iSheepsters/sheep-brain/sheepBrain/state.h

#ifndef _STATE_H
#define _STATE_H
#include "soundFile.h"

extern int msToNextSoundMin;
extern int msToNextSoundMax;

enum State {
  Bored,
  Attentive,
  Riding,
  ReadyToRide,
  NotInTheMood,
  Violated,
};

extern unsigned long timeEnteredCurrentState;

extern void setupState();
extern void updateState();
extern void logState();
extern boolean privateSensorEnabled();
class SheepState {
  public:
    virtual SheepState * update() = 0;
    const char * const name;
    const enum State state;
    uint16_t timeStateStarted = 0;
    unsigned long timeInState = 0;

    SoundCollection & ambientSounds;
    SoundCollection & getInitialSounds() {
      if (initialSounds.available()) return initialSounds;
      return ambientSounds;
    }
    SheepState(enum State st, const char * n, SoundCollection & s)
      : state(st), name(n), initialSounds(s), ambientSounds(s) {};
    SheepState(enum State st, const char * n, SoundCollection & s, SoundCollection & ambient)
      : state(st), name(n), initialSounds(s), ambientSounds(ambient) {};
    boolean playAmbientSound(unsigned long now);
  private:
    SoundCollection & initialSounds;

};

extern SheepState * currentSheepState;


class BoredState : public SheepState {
  public:
    BoredState() : SheepState(Bored, "Bored", boredSounds) {};
    SheepState * update();

};

class AttentiveState : public SheepState {
  public:
    AttentiveState() : SheepState(Attentive, "Attentive", firstTouchSounds, attentiveSounds) {};
    SheepState * update();
};

class ReadyToRideState : public SheepState {
  public:
    ReadyToRideState() : SheepState(ReadyToRide, "Ready to ride", readyToRideSounds) {};
    SheepState * update();
};

class RidingState : public SheepState {
  public:
    RidingState() : SheepState(Riding, "Riding", ridingSounds) {};

    SheepState * update();
};

class NotInTheMoodState : public SheepState {
  public:
    NotInTheMoodState() : SheepState(NotInTheMood, "Not in the mood", notInTheMoodSounds) {};
    SheepState * update();
};


class ViolatedState : public SheepState {
  public:
    ViolatedState() : SheepState(Violated, "Violated", violatedSounds) {};
    SheepState * update();
};

#endif
