iSheepsters/sheep-brain/sheepBrain/soundFile.cpp

#include <Arduino.h>
#include "soundFile.h"
#include "sound.h"
#include "printf.h"
#include "util.h"

//#include <MemoryFree.h>
#include <SPI.h>
#include <SdFat.h>

#define CARDCS          5     // Card chip select pin

int currentSoundPriority = 0;

const int PATH_BUFFER_LENGTH = 100;
char pathBuffer[PATH_BUFFER_LENGTH];

boolean isMusicFile(const char * name) {

  const char *suffix = strrchr(name, '.');
  if (name[0] == '_')
    return false;

  if (!allowRrated && (name[0] == 'r' || name[0] == 'R')) return false;
  if ( strcmp(suffix, ".MP3") == 0 || strcmp(suffix, ".mp3") == 0)
    return true;
  Serial.print("non-music file: \"");
  Serial.print(name);
  Serial.println("\"");
  return false;
}

SoundCollection::SoundCollection(uint8_t pri) : priority (pri) {
  strncpy(name, "", 13);
  count = 0;
}

boolean SoundCollection::loadCommon(const char * s) {
  strncpy(name, s, 13);
  myprintf(Serial, "opening %s\n", name);

  File dir = SD.open(name);
  myprintf(Serial, "opened %s\n", name);

  common = true;
  return load(dir);
}
char buf[FILE_NAME_LENGTH];

boolean SoundCollection::load(const char * s) {
  strncpy(name, s, 13);
  snprintf(buf, 30, "%d/%s", sheepNumber, name);
  myprintf(Serial, "opening %s\n", buf);
  File dir = SD.open(buf);
  bool result =  load(dir);
  if (result) {
    myprintf(Serial, "got %d sounds for %s\n", count, name);
  } else
    myprintf(Serial, "error loading sounds for %s\n", name);
  return result;
}



boolean SoundCollection::load(File dir, File script) {
  uint16_t i = 0;
  char txt[100];
  char *s = txt;
  File check;
  while (i < MAX_SOUND_FILES) {
    int len = script.fgets(txt, 100);
    if (len <= 0) break;
    if (txt[0] == '#')
      continue;
    char * term = strchr(txt, '\t');
    if (term != NULL)
      *term = '\0';
    else {
      term = strchr(txt, '\n');
      if (term != NULL)
        *term = '\0';
    }

    if (!isMusicFile(txt)) {
      myprintf(Serial, "Skipping non-music file \"%s\" from script\n", txt);
      continue;
    }
    if (check.open(&dir, s, O_READ)) {
      myprintf(Serial, "Loading #%d  \"%s\" from script, %d bytes\n", i, txt, check.fileSize());
      check.close();
      strncat(files[i].name, txt, FILE_NAME_LENGTH);
      files[i].collection = this;
      files[i].lastPlaying = 0;
      files[i].duration = 0;
      files[i].lastStarted = 0;
      i++;

    } else
      myprintf(Serial, "Could not open \"%s\" from script\n", txt);
  }
  script.close();
  count = i;
  scripted = true;
  nextFile = 0;
  return i > 0;
}

boolean SoundCollection::load(File dir) {
  count = 0;
  if (!dir.isDirectory()) {
    Serial.print(name);
    Serial.println(" is not a directory");
    dir.close();
    return false;
  }

  File script;
  if (script.open(&dir, "script.txt", O_READ)) {
    myprintf(Serial, "Loading script for %s\n", name);
    if (load(dir, script))
      return true;
  }

  Serial.println("Scanning all files");
  dir.rewind();
  uint16_t i = 0;
  char nm[30];
  while (i < MAX_SOUND_FILES) {
    File entry = dir.openNextFile();
    if (!entry) {
      break;
    }

    entry.getName(nm, 30);
    Serial.println(nm);
    if (!entry.isDirectory() && isMusicFile(nm)) {
      entry.getName(files[i].name, FILE_NAME_LENGTH);
      files[i].collection = this;
      files[i].lastPlaying = 0;
      files[i].duration = 0;
      files[i].lastStarted = 0;
      i++;
    }
    entry.close();
  }
  count = i;
  nextFile = 0;
  myprintf(Serial, "Found %d files for %s\n", count, name);
  // myprintf(Serial, "Free memory = %d\n", freeMemory());
  dir.close();
  return true;
}

void SoundCollection::list() {

  for (int i = 0; i < count; i++) {
    myprintf(Serial, "%s\n", files[i].name);
  }
}

uint16_t ago( unsigned long t,  unsigned long now) {
  return (now - t) / 1000;
}


void SoundCollection::verboseList(unsigned long now, boolean ambientSound) {


  Serial.println( "  duration   started   playing  eligable name");
  for (int i = 0; i < count; i++) {
    myprintf(Serial, "%10d%10d%10d     %s %d.mp3\n", files[i].duration, ago(files[i].lastStarted, now),
             ago(files[i].lastPlaying,  now),
             files[i].eligibleToPlay(now, ambientSound) ? " true" : "false",
             i);

  }
}

boolean soundPlayedRecently(unsigned long now) {
  return lastSoundPlaying + 10000L > now && now > 18000;
}

unsigned long nextVerboseList = 0;
boolean SoundCollection::playSound(unsigned long now, boolean ambientSound) {
  if (printInfo())
    myprintf(Serial, "trying to play sound for %s\n", name);
  if (ambientSound && soundPlayedRecently(now)) {
    if (printInfo()) {
      Serial.print("Too soon for any sound from ");
      Serial.println(name);
    }
    return false;
  }
  SoundFile *s = chooseSound(now, ambientSound);
  if (s == NULL) {
    if (ambientSound)
      Serial.print("No ambient sound found for ");
    else
      Serial.print("No sound found for ");
    Serial.println(name);


    myprintf(Serial, "Last sound %d\n", ago(lastSoundPlaying, now));
    if (nextVerboseList < now) {
      verboseList(now, ambientSound);
      nextVerboseList = now + 30000;
    }
    return false;
  };
  slowlyStopMusic();
  musicPlayerFullVolume();

  boolean result = false;
  if (common)
    result = playFile("%s/%s", name, s->name  );
  else
    result = playFile("%d/%s/%s", sheepNumber, name, s->name  );
  if (!result) {
    myprintf(Serial, "Could not start %s/%s\n", name, s->name  );
    musicPlayerNoVolume();
    return false;
  } else {
    if (printInfo())
      myprintf(Serial, "Starting %s/%s at %d\n", name, s->name, now);
    s->lastStarted = s->lastPlaying = now;
    currentSoundFile = s;
    currentSoundPriority = priority;
    return true;
  }

}


// If ambientSound is false, always return something
SoundFile * SoundCollection::leastRecentlyPlayed(unsigned long now,
    boolean ambientSound) {

  if (printInfo())
    myprintf(Serial, "finding least recently played %s\n", name);

  SoundFile * candidate = NULL;
  unsigned long bestTime = 0xfffffff;
  int offset = random(count);
  for (int i = 0; i < count; i++) {
    int index = (i + offset) % count;
    SoundFile *s = &(files[index]);
    if (s->lastPlaying == 0)
      return s;
    if (s->eligibleToPlay(now, ambientSound) && bestTime > s->lastPlaying) {
      candidate = s;
      bestTime = s->lastPlaying;
    }
  }
  if (candidate != NULL || ambientSound)
    return candidate;
  bestTime = 0xfffffff;
  for (int i = 0; i < count; i++) {
    int index = (i + offset) % count;
    SoundFile *s = &(files[index]);
    if (bestTime > s->lastPlaying) {
      candidate = s;
      bestTime = s->lastPlaying;
    }
  }
  return candidate;
}


SoundFile * SoundCollection::chooseSound(unsigned long now,  boolean ambientSound) {
  if (count == 0) return NULL;

  if (scripted) {
    if (printInfo()) {
      myprintf(Serial, "using script entry %d\n", nextFile);
    }
    SoundFile * f = &(files[nextFile]);
    nextFile++;
    if (nextFile >= count)
      nextFile = 0;
    return f;
  }

  if (this == & violatedSounds)
    ambientSound = false;
  if (random(3) <= 1) {
    // return first eligable sound
    int firstChoice = random(count);

    int i = firstChoice;
    while (true) {
      SoundFile *s = &(files[i]);
      if (s->eligibleToPlay(now, ambientSound))
        return s;

      i = (i + 1) % count;
      if (i == firstChoice) {
        break;
      }
    }
  }
  return leastRecentlyPlayed(now, ambientSound);
}

const boolean debug_eligible = false;
boolean SoundFile::eligibleToPlay(unsigned long now, boolean ambientSound) {
  if (now == 0) {
    if (debug_eligible) myprintf(Serial, "%s eligable, not played before\n", name);
    return true;
  }
  uint32_t minimumQuietTime = 10000;
  if (ambientSound && lastSoundPlaying + minimumQuietTime > now)
    return false;

  unsigned long d = duration;
  if (d == 0) d = 5000;

  uint32_t minimumRepeatTime = d * 2 + 120000L;

  boolean result = lastPlaying == 0 || lastPlaying + minimumRepeatTime < now;
  if (debug_eligible) { // list reasons
    if (result) {
      if (lastPlaying == 0)
        myprintf(Serial, "%s eligable: not played before\n",  name);
      else
        myprintf(Serial, "%s eligable: Last playing %d seconds ago; %d minimum\n",
                 name, (now - lastPlaying) / 1000, minimumRepeatTime / 1000);
      if (ambientSound) myprintf(Serial, "  last sound %d seconds ago, minimum quiet %d seconds\n",
                                   (now - lastSoundPlaying) / 1000, minimumQuietTime / 1000);
    } else if (false) {
      myprintf(Serial, "%s not eligable: Last playing %d seconds ago; %d minimum\n",
               name, (now - lastPlaying) / 1000, minimumRepeatTime / 1000);
      if (ambientSound) myprintf(Serial, "  last sound %d seconds ago, minimum quiet %d seconds\n",
                                   (now - lastSoundPlaying) / 1000, minimumQuietTime / 1000);

    }
  }
  return result;
}


SoundFile * currentSoundFile = NULL;

#define CARDCS 5
#define SPI_SPEED SD_SCK_MHZ(4)

boolean setupSD() {
  if (!SD.begin(CARDCS, SPI_SPEED)) {
    Serial.println(F("SD failed, or not present"));
    if (SD.card()->errorCode()) {
      Serial.println(
        F( "\nSD initialization failed.\n"
           "Do not reformat the card!\n"
           "Is the card correctly inserted?\n"
           "Is chipSelect set to the correct value?\n"
           "Does another SPI device need to be disabled?\n"
           "Is there a wiring/soldering problem?\n"));

      Serial.println(int(SD.card()->errorCode()));
      Serial.println(int(SD.card()->errorData()));
      return false;
    }
  }

  Serial.println("SD OK!");
  myprintf(Serial, "size of SoundFile is %d\n", sizeof(SoundFile));


  // list files
  // printDirectory(SD.open("/"), 0);
  return true;
}




/// File listing helper
void printDirectory(File dir, int numTabs) {
  while (true) {
    char buf[40];
    File entry = dir.openNextFile();
    if (! entry) {
      // no more files
      //Serial.println("**nomorefiles**");
      break;
    }
    for (uint8_t i = 0; i < numTabs; i++) {
      Serial.print('\t');
    }
    entry.getName(buf, 40);
    Serial.print(buf);
    if (entry.isDirectory()) {
      Serial.println("/");
      printDirectory(entry, numTabs + 1);
    } else {
      // files have sizes, directories do not
      Serial.print("\t\t");
      Serial.println(entry.size(), DEC);
    }
    entry.close();
  }
}

void loadPerSheepSounds() {
  Serial.println("Loading sound files");
  //myprintf(Serial, "Free memory = %d\n", freeMemory());
  boredSounds.load("BORED");
  generalSounds.load("GENERAL");
  firstTouchSounds.load("TOUCHED");
  attentiveSounds.load("ATTNT");
  
    ridingSounds.load("RIDNG");
    readyToRideSounds.load("RDRID");
    endOfRideSounds.load("EORID");
    notInTheMoodSounds.load("NMOOD");
    violatedSounds.load("VIOLT");
    inappropriateTouchSounds.load("INAPP");
    seperatedSounds.load("SEPRT");
  
 // myprintf(Serial, "Free memory = %d\n", freeMemory());

}
