iSheepsters/sheep-brain/sheepBrain/comm.cpp

#include <Arduino.h>
#include <Wire.h>
#include "comm.h"
#include "printf.h"
#include "Print.h"
#include "util.h"
#include "touchSensors.h"
#include "scheduler.h"


const uint8_t commAddress = 0x44;

const uint8_t rebootStarted = 255;
const uint8_t rebootActivity = 254;

CommData commData;
ActivityData activityData;
unsigned long nextComm = 0;
uint8_t lastActivity = 0;

void setupComm() {
  commData.sheepNum = sheepNumber;
  addScheduledActivity(100, sendComm, "comm");
}


void getLastActivity() {

  int received = Wire.requestFrom(commAddress, sizeof(ActivityData));
  myprintf(Serial, "Requesting last activity, received %d bytes\n", received);
  activityData.reboots = 17;
  uint8_t * p = (uint8_t *) & activityData;
  if (received != sizeof(ActivityData)) {
    myprintf(Serial, "Expected %d bytes\n", sizeof(ActivityData));
    return;
  }
  for (int i = 0; i < received; i++)
    * (p++) = Wire.read();
  myprintf(Serial, "%d reboots, %d lastActivity, %d lastSubActivity\n",
           activityData.reboots,
           activityData.lastActivity,
           activityData. subActivity);
  myprintf(Serial, "%d seconds since last activity, %d seconds since slave reboot\n",
           activityData. secondsSinceLastActivity,
           activityData. secondsSinceBoot);
}

void sendBoot() {
  Serial.println("Sending boot");
  sendActivity(rebootStarted);
  delay(1);
  sendActivity(rebootActivity);
}

volatile uint8_t currentSubActivity;
uint8_t sendActivity(uint8_t activity) {
  if (activity == lastActivity && currentSubActivity == 0)
    return 0;
  lastActivity = activity;
  currentSubActivity = 0;
  Wire.beginTransmission(commAddress);
  Wire.write(57);
  Wire.write(activity);
  Wire.write(0);
  uint8_t result = Wire.endTransmission();
  return result;
}

uint8_t sendSubActivity(uint8_t subActivity) {
  currentSubActivity = subActivity;
  Wire.beginTransmission(commAddress);
  Wire.write(57);
  Wire.write(lastActivity);
  Wire.write(subActivity);
  uint8_t result = Wire.endTransmission();
  return result;
}

void sendComm() {

  unsigned long now = millis();
  if (  commData.state != currentSheepState->state
        || commData.currTouched != currTouched
        || nextComm < now) {
    nextComm = now + 1000;
 
    commData.state = currentSheepState->state;
    uint8_t touched = currTouched;
    if (sheepNumber == 9 || sheepNumber == 13) {

      uint8_t t = swapLeftRightSensors(touched);
      //myprintf(Serial, "touch %02x -> %02x\n", touched, t);
      touched = t;
    }
    commData.currTouched = touched;

      commData.backTouchQuality = millisToSecondsCapped(qualityTime(BACK_SENSOR));
    commData.headTouchQuality = millisToSecondsCapped(qualityTime(HEAD_SENSOR));
    commData.activated =  isActive() ? Active : Inactive ;
    uint8_t * p = (uint8_t *)&commData;
    if (false) {
      Serial.print("Sending ");
      for (int i = 0; i < sizeof(CommData); i++) {
        myprintf(Serial, "%02x ", p[i]);
      }
      Serial.println();
    }

    noInterrupts();
    Wire.beginTransmission(commAddress);

    Wire.write(42); // check byte
    Wire.write(p, sizeof(CommData));

    Wire.flush();
    uint8_t result = Wire.endTransmission();
    interrupts();
    delay(1);
    return;
  }
}

/**
   I2C_ClearBus
   (http://www.forward.com.au/pfod/ArduinoProgramming/I2C_ClearBus/index.html)
   (c)2014 Forward Computing and Control Pty. Ltd.
   NSW Australia, www.forward.com.au
   This code may be freely used for both private and commerical use
*/

/**
   This routine turns off the I2C bus and clears it
   on return SCA and SCL pins are tri-state inputs.
   You need to call Wire.begin() after this to re-enable I2C
   This routine does NOT use the Wire library at all.

   returns 0 if bus cleared
           1 if SCL held low.
           2 if SDA held low by slave clock stretch for > 2sec
           3 if SDA held low after 20 clocks.
*/
int I2C_ClearBus() {
#if defined(TWCR) && defined(TWEN)
  TWCR &= ~(_BV(TWEN)); //Disable the Atmel 2-Wire interface so we can control the SDA and SCL pins directly
#endif

  pinMode(SDA, INPUT_PULLUP); // Make SDA (data) and SCL (clock) pins Inputs with pullup.
  pinMode(SCL, INPUT_PULLUP);

  delay(500);  // Wait 2.5 secs. This is strictly only necessary on the first power
  // up of the DS3231 module to allow it to initialize properly,
  // but is also assists in reliable programming of FioV3 boards as it gives the
  // IDE a chance to start uploaded the program
  // before existing sketch confuses the IDE by sending Serial data.

  boolean SCL_LOW = (digitalRead(SCL) == LOW); // Check is SCL is Low.
  if (SCL_LOW) { //If it is held low Arduno cannot become the I2C master.
    return 1; //I2C bus error. Could not clear SCL clock line held low
  }

  boolean SDA_LOW = (digitalRead(SDA) == LOW);  // vi. Check SDA input.
  int clockCount = 20; // > 2x9 clock

  while (SDA_LOW && (clockCount > 0)) { //  vii. If SDA is Low,
    clockCount--;
    // Note: I2C bus is open collector so do NOT drive SCL or SDA high.
    pinMode(SCL, INPUT); // release SCL pullup so that when made output it will be LOW
    pinMode(SCL, OUTPUT); // then clock SCL Low
    delayMicroseconds(10); //  for >5uS
    pinMode(SCL, INPUT); // release SCL LOW
    pinMode(SCL, INPUT_PULLUP); // turn on pullup resistors again
    // do not force high as slave may be holding it low for clock stretching.
    delayMicroseconds(10); //  for >5uS
    // The >5uS is so that even the slowest I2C devices are handled.
    SCL_LOW = (digitalRead(SCL) == LOW); // Check if SCL is Low.
    int counter = 20;
    while (SCL_LOW && (counter > 0)) {  //  loop waiting for SCL to become High only wait 2sec.
      counter--;
      delay(100);
      SCL_LOW = (digitalRead(SCL) == LOW);
    }
    if (SCL_LOW) { // still low after 2 sec error
      return 2; // I2C bus error. Could not clear. SCL clock line held low by slave clock stretch for >2sec
    }
    SDA_LOW = (digitalRead(SDA) == LOW); //   and check SDA input again and loop
  }
  if (SDA_LOW) { // still low
    return 3; // I2C bus error. Could not clear. SDA data line held low
  }

  // else pull SDA line low for Start or Repeated Start
  pinMode(SDA, INPUT); // remove pullup.
  pinMode(SDA, OUTPUT);  // and then make it LOW i.e. send an I2C Start or Repeated start control.
  // When there is only one I2C master a Start or Repeat Start has the same function as a Stop and clears the bus.
  /// A Repeat Start is a Start occurring after a Start with no intervening Stop.
  delayMicroseconds(10); // wait >5uS
  pinMode(SDA, INPUT); // remove output low
  pinMode(SDA, INPUT_PULLUP); // and make SDA high i.e. send I2C STOP control.
  delayMicroseconds(10); // x. wait >5uS
  pinMode(SDA, INPUT); // and reset pins as tri-state inputs which is the default state on reset
  pinMode(SCL, INPUT);
  return 0; // all ok
}
