iSheepsters/sheep-brain/project/documentation/ESP32/datasheet F000905/Onboard OLED screen data/0.96 inch OLED C language screen driver/codetab.h

/************************************************************************************
*  Copyright (c), 2015, HelTec Automatic Technology co.,LTD.
*            All rights reserved.
*
* Http:    www.heltec.cn
* Email:   cn.heltec@gmail.com
* WebShop: heltec.taobao.com
*
* File name: OLED.h
* Project  : OLED
* Processor: STC89C52
* Compiler : Keil C51 Compiler
* 
* Author : Aaron Lee
* Version: 1.00
* Date   : 2014.3.24
* Email  : hello14blog@gmail.com
* Modification: none
* 
* Description:
* 1. 128*64点整OLED模块功能演示程序的字表，仅适用heltec.taobao.com所售产品;
* 2. 字表由打包资料中的“取字软件”计算得出;
* 3. 取字方式 -- 共阴、列行式、逆向输出
*
* Others: none;
*
* Function List: none;
*
* History: none;
*
*************************************************************************************/

/***************************16*16的点阵字体取模方式：共阴——列行式——逆向输出*********/
unsigned char code F16x16[] = 	  	 
{
0x00,0x02,0x02,0xFA,0xFA,0xAA,0xAA,0xFF,0xFF,0xAA,0xAA,0xFA,0xFA,0x02,0x02,0x00,
0x00,0x42,0x72,0x72,0x3A,0x7A,0x42,0x4B,0x5B,0x52,0x62,0x62,0x13,0x77,0x66,0x00,/*"惠",0*/

0x20,0x3C,0x1C,0xFF,0xFF,0xB0,0xB4,0x24,0x24,0x3F,0x3F,0xE4,0xE4,0x24,0x24,0x20,
0x02,0x02,0x03,0xFF,0xFF,0x00,0x01,0x05,0x1D,0x59,0xC1,0xFF,0x7F,0x01,0x01,0x01,/*"特",1*/

0x00,0x00,0x00,0xF8,0xF8,0x48,0x4C,0x4F,0x4B,0x4A,0x48,0x48,0xF8,0xF8,0x00,0x00,
0x00,0x00,0x00,0xFF,0xFF,0x44,0x44,0x44,0x44,0x44,0x44,0x44,0xFF,0xFF,0x00,0x00,/*"自",2*/

0x20,0x24,0x24,0xE4,0xE4,0x24,0x24,0x24,0x30,0x10,0xFF,0xFF,0x10,0xF0,0xF0,0x00,
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
	0x06,0x06,0x06,0x06,0x06,0x00,0x00,0x06,0x06,0x06,0x06,0x06,0x00,0x00,0x06,0x06,
	0x06,0x06,0x06,0x00,0x00,0x06,0x06,0x06,0xE6,0x66,0x20,0x00,0x06,0x06,0x86,0x06,
	0x06,0x00,0x00,0x06,0x06,0x06,0x06,0x86,0x00,0x00,0x06,0x06,0x06,0x06,0x06,0x00,
	0x00,0x86,0x86,0x86,0x86,0x86,0x80,0x80,0x86,0x86,0x06,0x86,0x86,0xC0,0xC0,0x86,
	0x86,0x86,0x06,0x06,0xD0,0x30,0x76,0x06,0x06,0x06,0x06,0x00,0x00,0x06,0x06,0x06,
	0x06,0x06,0x00,0x00,0x06,0x06,0x06,0x06,0x06,0x00,0x00,0x06,0x06,0x06,0x06,0x06,
	0x00,0x00,0x06,0x06,0x06,0x06,0x06,0x00,0x00,0x00,0x00,0x00,0x00,0x00,0x00,0x00,
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
	0x80,0xFF,0x80,0xEE,0xEE,0xEE,0xF5,0xFB,0xFF,0x9C,0xBE,0xB6,0xB6,0x88,0xFF,0x00,/*"D:\DreamSpark\OLED\MP3_UI.bmp",0*/
};
