iSheepsters/sheep-brain/project/src/main.c

// #include "emotion-controller.h"
// #include <Arduino.h>
#include "emotion-controller.h"

// EmotionController emotionController;

void setup() {
  // emotionController.Init();
}

void loop() {
  // emotionController.update();
}
