iSheepsters/sheep-brain/sheepSlaveBrain/all.h

#ifndef _ALL_H
#define _ALL_H

#include <FastLED.h>

const uint8_t GRID_HEIGHT = 25;
const uint8_t QUARTER_GRID_WIDTH = 8;
const uint8_t HALF_GRID_WIDTH = 16;
const uint8_t GRID_WIDTH = 2 * HALF_GRID_WIDTH;

enum State {
  Bored,
  Attentive,
  Riding,
  ReadyToRide,
  NotInTheMood,
  Violated,
};

enum ActiveState {
  Off, Inactive, Active
};

struct __attribute__ ((packed)) CommData {
  CommData() : sheepNum(0), state(Bored),
    currTouched(0), activated(Active) {};

  uint8_t sheepNum;
  enum State state;
  uint8_t currTouched;
  uint8_t backTouchQuality; // seconds
  uint8_t headTouchQuality; // seconds
  enum ActiveState activated;
};

extern CommData commData;

extern CRGB & getSheepLEDFor(uint8_t x, uint8_t y);

extern CRGB leds[];
extern volatile boolean animationsSetUp;
extern void setupSchedule();

#endif
