iSheepsters/sheep-brain/sheepBrain/soundFile.h

#ifndef _SOUNDFILE_H
#define _SOUNDFILE_H
#include <SdFat.h>

extern boolean setupSD();
extern void printDirectory(File dir, int numTabs);
extern boolean soundPlayedRecently(unsigned long now);

extern void loadPerSheepSounds();
class SoundCollection;
const uint8_t MAX_SOUND_FILES = 18;
const uint8_t FILE_NAME_LENGTH = 30; 

class SoundFile {
  public:
    SoundFile() : lastStarted(0), lastPlaying(0), duration(0) {
      name[0] = 0;
    };

    uint32_t lastStarted;
    uint32_t lastPlaying;
    uint32_t duration;
    SoundCollection * collection;
    char name[FILE_NAME_LENGTH];
    boolean eligibleToPlay(unsigned long now,  boolean ambientSound);
};

class SoundCollection {
  public:
    SoundCollection(uint8_t pri);
    char name[13];
    uint16_t count;
    boolean common = false;
    boolean scripted = false;
    boolean available() {
      return count>0;
    }
    uint8_t nextFile = 0;
    const uint8_t priority; // higher priority sounds will preempt lower priority sounds
    SoundFile files[MAX_SOUND_FILES];


    void list();
    void verboseList(unsigned long now,  boolean ambientSound);

    boolean load(const char * s);
    boolean loadCommon(const char * s);
    boolean load(File f);
    boolean load(File f, File script);
    SoundFile * chooseSound(unsigned long now,  boolean ambientSound);
    SoundFile * leastRecentlyPlayed(unsigned long now, boolean ambientSound);
    boolean playSound(unsigned long now,  boolean ambientSound);

};


extern SoundFile * currentSoundFile;
extern int currentSoundPriority;

extern unsigned long nextAmbientSound;
extern unsigned long nextBaa;

extern SoundCollection generalSounds;
extern SoundCollection boredSounds;
extern SoundCollection firstTouchSounds;
extern SoundCollection ridingSounds;
extern SoundCollection readyToRideSounds;
extern SoundCollection endOfRideSounds;
extern SoundCollection attentiveSounds;
extern SoundCollection notInTheMoodSounds;
extern SoundCollection violatedSounds;
extern SoundCollection changeSounds;
extern SoundCollection inappropriateTouchSounds;
extern SoundCollection seperatedSounds;
extern SoundCollection baaSounds;

#endif
